gavinlyonsrepo/Arduino_Clock_2/doc/eagle/clock2.sch

## EAGLE design doc/eagle/clock2.sch (2019-02-07)

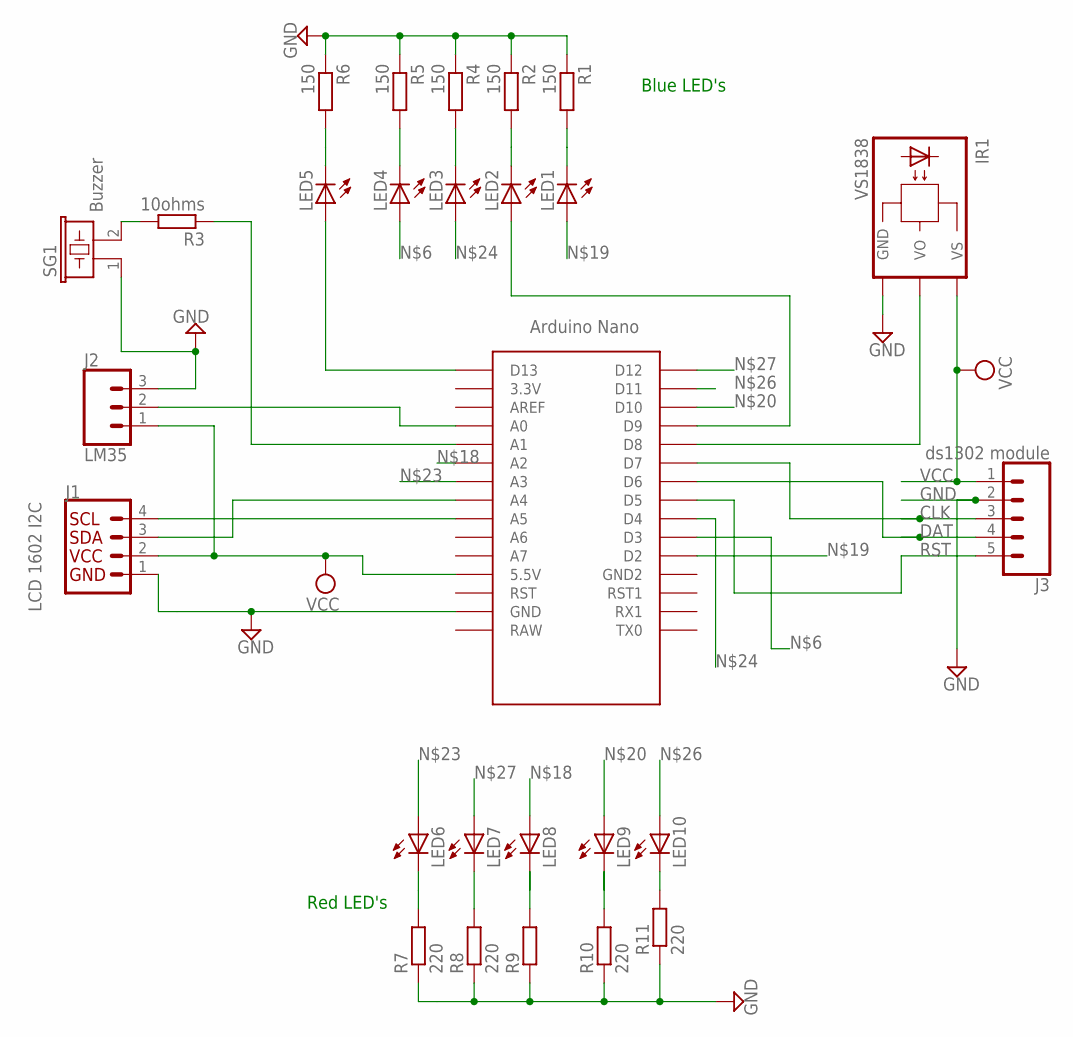
[picture p6: schematic clock2.sch]

Parts:
IR1: VS1838; TSOP17_TB1
J1: LCD 1602 I2C; 1X04
J2: LM35; 1X03
J3: ds1302 module; 1X05
LED1, LED2, LED3, LED4, LED5, LED6, LED7, LED8, LED9, LED10: LED5MM
R1, R2, R4, R5, R6: 150; 0204/7
R3: 10ohms; 0204/7
R7, R8, R10, R11: 220; 0204/7
R9: R0204/7; 0204/7
SG1: Buzzer; B/C17L
U$1: NANO

Connections:
CLK: J3.3, U$1.D7
DAT: J3.4, U$1.D6
GND: IR1.GND, J1.1, J2.3, J3.2, R1.1, R2.1, R4.1, R5.1, R6.1, R7.1, R8.1, R9.1, R10.1, R11.1, SG1.1, U$1.GND
unnamed: R3.1, U$1.A1
unnamed: R3.2, SG1.2
unnamed: J1.4, U$1.A5
unnamed: J1.3, U$1.A4
unnamed: IR1.VO, U$1.D8
unnamed: LED4.A, U$1.D3
unnamed: LED10.K (C), R11.2
unnamed: J2.2, U$1.A0
unnamed: LED9.K (C), R10.2
unnamed: LED8.K (C), R9.2
unnamed: LED7.K (C), R8.2
unnamed: LED6.K (C), R7.2
unnamed: LED5.K (C), R6.2
unnamed: LED4.K (C), R5.2
unnamed: LED3.K (C), R4.2
unnamed: LED2.K (C), R2.2
unnamed: LED1.K (C), R1.2
unnamed: LED5.A, U$1.D13
unnamed: LED3.A, U$1.D4
unnamed: LED7.A, U$1.D12
unnamed: LED2.A, U$1.D9
RST: J3.5, U$1.D5
VCC: IR1.VS, J1.2, J2.1, J3.1, U$1.5V (5.5V)

Notes on the sheet:
Red LED's
Blue LED's
